envenomator/calculator/code/include/FreeMono8pt7b.h

const uint8_t FreeMono8pt7bBitmaps[] PROGMEM = {
  0xFE, 0x40, 0x49, 0x24, 0x92, 0x48, 0x14, 0x28, 0x53, 0xF2, 0x44, 0xBF,
  0x94, 0x28, 0x50, 0x00, 0x10, 0x79, 0x12, 0x03, 0x80, 0xC0, 0xC3, 0xFC,
  0x20, 0x30, 0x91, 0x21, 0x80, 0x67, 0x13, 0x09, 0x12, 0x18, 0x39, 0x04,
  0x10, 0x62, 0x59, 0x62, 0x74, 0x49, 0x24, 0x1A, 0xAA, 0xA5, 0x29, 0x55,
  0x6A, 0x20, 0x82, 0x7E, 0x51, 0x20, 0x21, 0x09, 0xF2, 0x10, 0x80, 0x6B,
  0x48, 0xFE, 0xF0, 0x04, 0x10, 0x82, 0x10, 0x42, 0x08, 0x21, 0x04, 0x20,
  0x31, 0x28, 0x61, 0x86, 0x18, 0x61, 0x48, 0xC0, 0x23, 0x28, 0x42, 0x10,
  0x84, 0x27, 0xC0, 0x7B, 0x28, 0x41, 0x08, 0x23, 0x10, 0x83, 0xF0, 0xF8,
  0x18, 0x10, 0x21, 0x80, 0x80, 0x81, 0x84, 0xF0, 0x08, 0xE2, 0x92, 0x49,
  0x28, 0x9F, 0x08, 0x70, 0x78, 0x81, 0x03, 0xE4, 0x60, 0x40, 0x81, 0xC4,
  0x70, 0x3D, 0x84, 0x20, 0xBB, 0x38, 0x61, 0x4C, 0xE0, 0xFC, 0x10, 0x42,
  0x08, 0x21, 0x04, 0x10, 0x80, 0x7B, 0x38, 0x61, 0x79, 0x28, 0x61, 0xCD,
  0xE0, 0x79, 0x8A, 0x0C, 0x1C, 0x6F, 0x40, 0x82, 0x09, 0xE0, 0xF0, 0x3C,
  0x6C, 0x00, 0xD6, 0x80, 0x02, 0x18, 0xC6, 0x06, 0x03, 0x01, 0x80, 0xFF,
  0x00, 0xFF, 0x40, 0x60, 0x30, 0x10, 0xC2, 0x18, 0x00, 0x7A, 0x10, 0x43,
  0x18, 0x80, 0x00, 0x30, 0x38, 0x8A, 0x14, 0xEB, 0x54, 0xA9, 0x4F, 0x80,
  0x80, 0xF0, 0x38, 0x0A, 0x05, 0x04, 0x42, 0x21, 0xF1, 0x04, 0x82, 0xE3,
  0x80, 0xFC, 0x42, 0x42, 0x42, 0x7C, 0x43, 0x41, 0x41, 0xFE, 0x3D, 0x43,
  0x81, 0x80, 0x80, 0x80, 0xC0, 0x61, 0x3E, 0xFC, 0x42, 0x41, 0x41, 0x41,
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
  {   241,   8,   9,  10,    1,   -8 },   // 0x46 'F'
  {   250,   9,   9,  10,    1,   -8 },   // 0x47 'G'
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

const GFXfont FreeMono8pt7b PROGMEM = {
  (uint8_t  *)FreeMono8pt7bBitmaps,
  (GFXglyph *)FreeMono8pt7bGlyphs,
  0x20, 0x7E, 16 };

// Approx. 1347 bytes
