envenomator/calculator/code/include/FreeMono7pt7b.h

const uint8_t FreeMono7pt7bBitmaps[] PROGMEM = {
  0xFC, 0x80, 0xB6, 0xD0, 0x28, 0xA2, 0x9F, 0x2B, 0xF2, 0x8E, 0x30, 0x00,
  0x10, 0xE4, 0x90, 0x38, 0x18, 0x7E, 0x10, 0x71, 0x24, 0x9C, 0x1F, 0xF2,
  0x49, 0x1C, 0x39, 0x04, 0x08, 0xE6, 0x68, 0x9F, 0xF0, 0x6A, 0xAA, 0x50,
  0xA5, 0x56, 0xA0, 0x13, 0x53, 0x8C, 0x48, 0x21, 0x3E, 0x42, 0x00, 0x6B,
  0x40, 0xFC, 0xC0, 0x08, 0x84, 0x22, 0x11, 0x08, 0x44, 0x00, 0x72, 0xA3,
  0x18, 0xC6, 0x2A, 0x70, 0x59, 0x24, 0x97, 0x7B, 0x38, 0x41, 0x08, 0x46,
  0x20, 0x7C, 0xF0, 0x20, 0x82, 0x30, 0x20, 0x63, 0x78, 0x13, 0x95, 0x29,
  0x4B, 0xE2, 0x38, 0x79, 0x04, 0x1E, 0x44, 0x10, 0x63, 0x78, 0x3D, 0x8C,
  0x2E, 0xCE, 0x18, 0x53, 0x38, 0xFC, 0x10, 0x82, 0x08, 0x41, 0x04, 0x20,
  0x74, 0x63, 0x17, 0x6E, 0x31, 0x70, 0x73, 0x28, 0x61, 0xCD, 0xD0, 0xC6,
  0xF0, 0xC0, 0x30, 0x60, 0x06, 0xB4, 0x04, 0x66, 0x10, 0x30, 0x30, 0xFE,
  0x03, 0xF8, 0x40, 0xC0, 0x83, 0x11, 0x80, 0x74, 0x42, 0x22, 0x00, 0x04,
  0x38, 0x8A, 0x14, 0xEA, 0x54, 0xA7, 0xC0, 0x40, 0x78, 0x78, 0x18, 0x24,
  0x24, 0x24, 0x3E, 0x42, 0xE7, 0xF8, 0x89, 0x13, 0xC4, 0x68, 0x50, 0xFE,
  0x3A, 0x8E, 0x0C, 0x08, 0x10, 0x10, 0x1F, 0xFC, 0x42, 0x41, 0x41, 0x41,
  0x41, 0x42, 0xFC, 0xFC, 0x89, 0x43, 0x85, 0x08, 0x10, 0xFF, 0xFE, 0x85,
  0x43, 0x85, 0x08, 0x10, 0x70, 0x3A, 0x46, 0x80, 0x80, 0x87, 0x82, 0x42,
  0x3C, 0xEE, 0x89, 0x13, 0xE4, 0x48, 0x91, 0x77, 0xE9, 0x24, 0x97, 0x1E,
  0x08, 0x10, 0x20, 0x50, 0xA3, 0x3C, 0xE6, 0x44, 0x48, 0x50, 0x68, 0x44,
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
  {   190,   7,   8,   8,    1,   -7 },   // 0x46 'F'
  {   197,   8,   8,   8,    1,   -7 },   // 0x47 'G'
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

const GFXfont FreeMono7pt7b PROGMEM = {
  (uint8_t  *)FreeMono7pt7bBitmaps,
  (GFXglyph *)FreeMono7pt7bGlyphs,
  0x20, 0x7E, 14 };

// Approx. 1201 bytes
