envenomator/calculator/code/src/status.cpp

#include "status.h"

status::status(uint32_t value, status::Base base, uint8_t bitlength, bool sign)
{
    _value = value;
    _base = base;
    _bitlength = bitlength;
    _sign = sign;
}

uint32_t status::getValue()
{
    return _value;
}

void status::setValue(uint32_t value)
{
    _value = value;
    _clipToBitLength();
}

void status::_clipToBitLength()
{
    switch(_bitlength)
    {
        case 8:
            _value = _value & 0xFF;
            break;
        case 16:
            _value = _value & 0xFFFF;
            break;
        case 32:
            _value = _value & 0xFFFFFFFF;
            break;
    }
}

uint32_t status::clipToBitLength(uint32_t value, uint8_t bitlength)
{
    uint32_t temp;

    switch(bitlength)
    {
        case 8:
            temp = value & 0xFF;
            break;
        case 16:
            temp = value & 0xFFFF;
            break;
        case 32:
            temp = value & 0xFFFFFFFF;
            break;
    }
    return temp;
}

void status::setBase(status::Base base)
{
    _base = base;
}

status::Base status::getBase()
{
    return _base;
}

void status::setBitLength(uint8_t bitlength)
{
    _bitlength = bitlength;
    _clipToBitLength();
}

uint8_t status::getBitLength()
{
    return _bitlength;
}

bool status::isNegative(uint32_t value, uint8_t bitlength)
{
    switch(bitlength)
    {
        case 8:
            return value & 0x80;
            break;
        case 16:
            return value & 0x8000;
            break;
        case 32:
            return value & 0x80000000;
            break;
        default:
            break;
    }
    return false;
}

bool status::hasCarry(uint64_t value, uint8_t bitlength)
{
    switch(bitlength)
    {
        case 8:
            return value & 0x100;
            break;
        case 16:
            return value & 0x10000;
            break;
        case 32:
            return value & 0x100000000;
            break;
        default:
            break;
    }
    return false;
}

void status::setSign(bool sign)
{
    _sign = sign;
}

bool status::getSign()
{
    return _sign;
}
