envenomator/calculator/code/include/inputbox.h

#ifndef INPUTBOX_H
#define INPUTBOX_H

#include <stdint.h>
#include "displayvalue.h"

class inputBox: public displayValue
{
    public:
        inputBox(uint32_t value, Base base, uint8_t bitlength, bool sign): displayValue(value, base, bitlength, sign) {}
        void processKeyValue(unsigned char val);
        void negateDisplay();         // negates the current input value.
        void deleteDigit();

    private:
        void _flashWarning();
        void _negateValue();         // negates the current input value.
};

#endif
